oxda/usb-cereal/img/usb-cereal-annotated.jpg

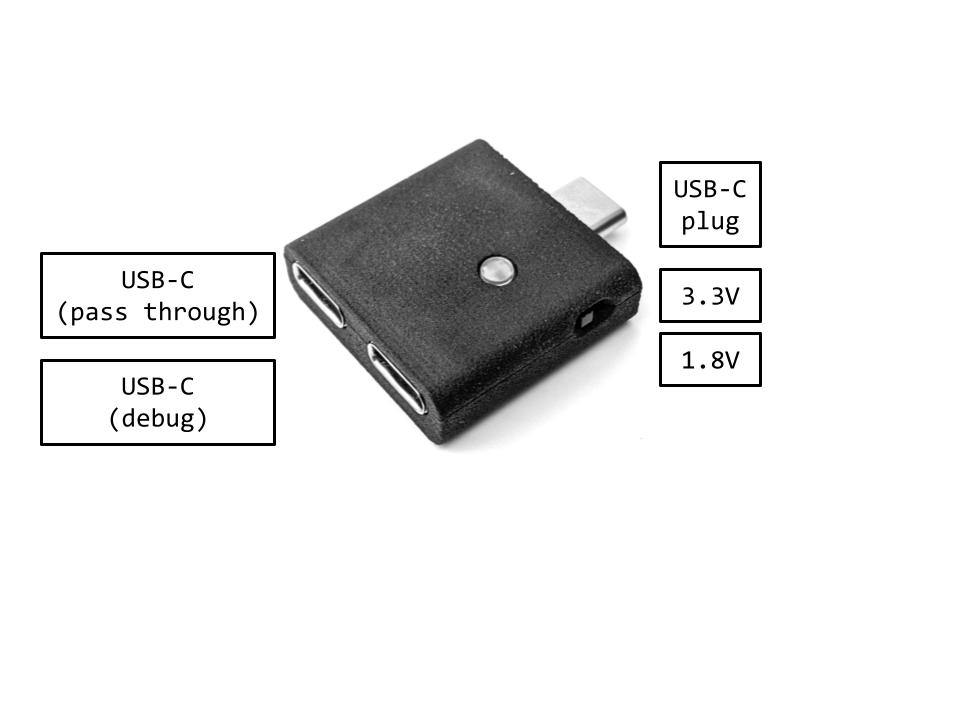
img/usb-cereal-annotated.jpg
